M-oster/Advanced-Ultimate-Box-Maker/Examples/Mini-PowerSupply/stls/Adv-Ultimate-Box-PowerSupply-Frontpanel.stl

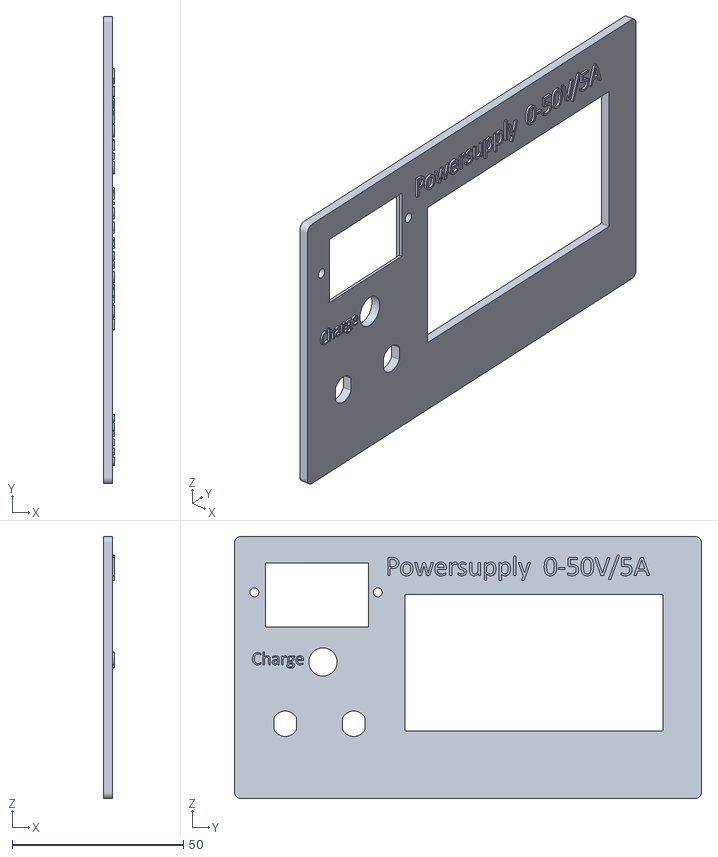
[picture p26: CAD file, 2021-09-02]
Examples/Mini-PowerSupply/stls/Adv-Ultimate-Box-PowerSupply-Frontpanel.stl
3.10 x 136.2 x 76.4
