M-oster/Advanced-Ultimate-Box-Maker/Examples/Mini-PowerSupply/assemblies/dc-dc-5a-cc.FCStd

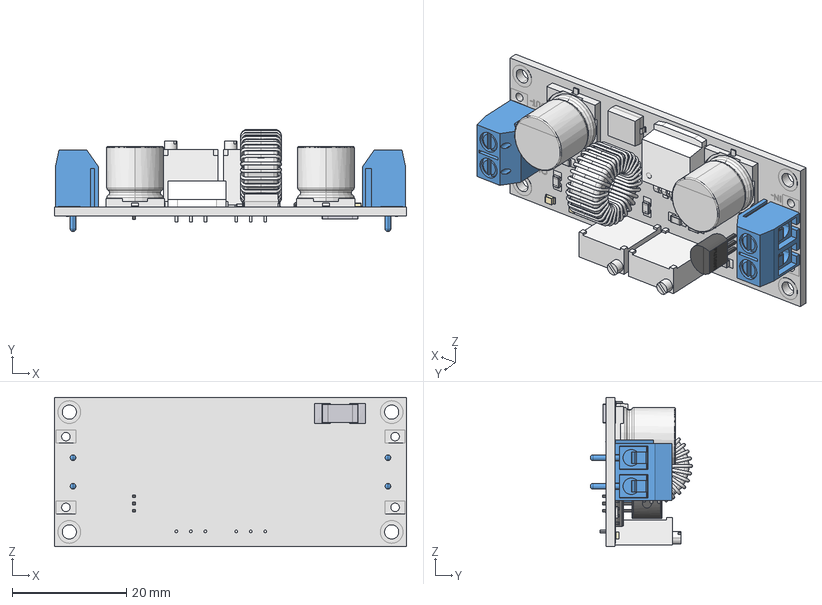
[picture p27: CAD file, 2021-09-02]
Examples/Mini-PowerSupply/assemblies/dc-dc-5a-cc.FCStd
61.7 x 17.9 x 26.2 mm
PCB^dc-dc-5a-cc
DG301-5.0-02
Trimpot 3296W_Valor predeterminado
Trimpot 3296W_Valor predeterminado001
CAPACITOR 10x10 SMD
CAPACITOR 10x10 SMD001
XL4015E1_® 㬮«砭¨뾀
LM317LZ
coil^dc-dc-5a-cc
C
C001
C002
R
R001
R002
R003
R004
LED
LED001
LED002
D
R005
R006
R007
C003
SO-8
Rshunt^dc-dc-5a-cc
DG301-5.0-003
