M-oster/Advanced-Ultimate-Box-Maker/Examples/Mini-PowerSupply/stls/Adv-Ultimate-Box-PowerSupply-Backpanel.stl

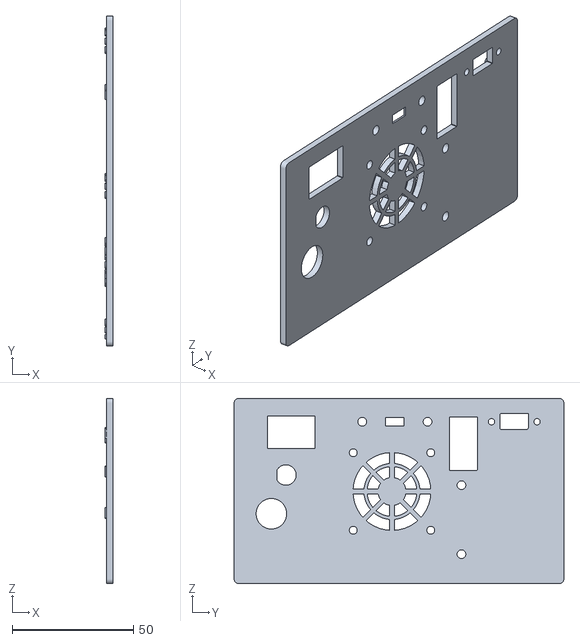
[picture p28: CAD file, 2021-09-02]
Examples/Mini-PowerSupply/stls/Adv-Ultimate-Box-PowerSupply-Backpanel.stl
3.10 x 136.2 x 76.4
