M-oster/Advanced-Ultimate-Box-Maker/Examples/Mini-PowerSupply/assemblies/Relais-Holder.step

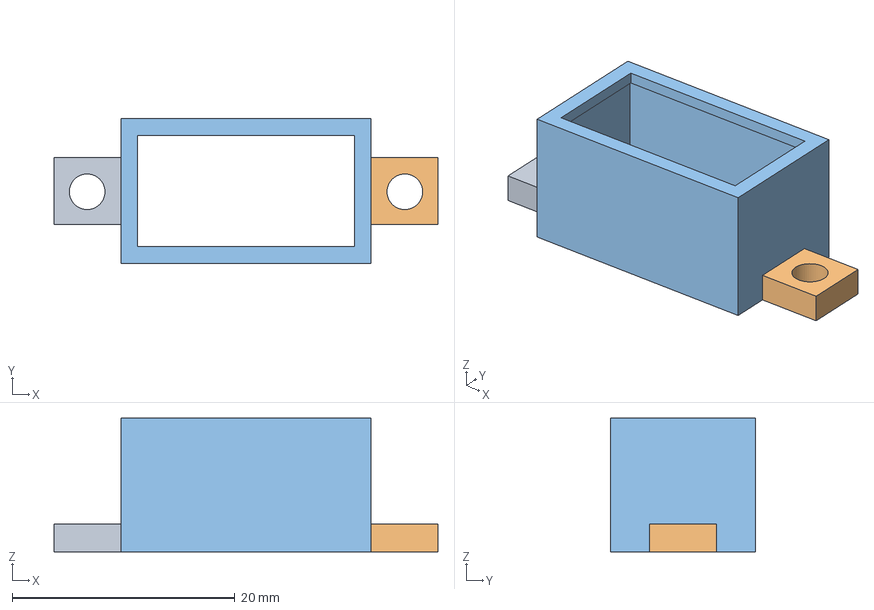
[picture p29: CAD file, 2021-09-02]
Examples/Mini-PowerSupply/assemblies/Relais-Holder.step
34.5 x 13.0 x 12.0 mm
