M-oster/Advanced-Ultimate-Box-Maker/Examples/Mini-PowerSupply/assemblies/LED_5mm+Socket.3mf

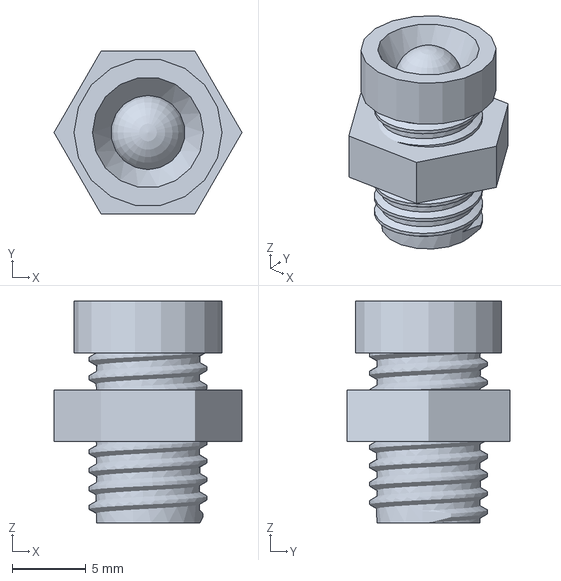
[picture p30: CAD file, 2021-09-02]
Examples/Mini-PowerSupply/assemblies/LED_5mm+Socket.3mf
12.7 x 11.0 x 15.0 mm
