M-oster/Advanced-Ultimate-Box-Maker/Examples/Mini-PowerSupply/assemblies/BT-Modul_BK3231.step

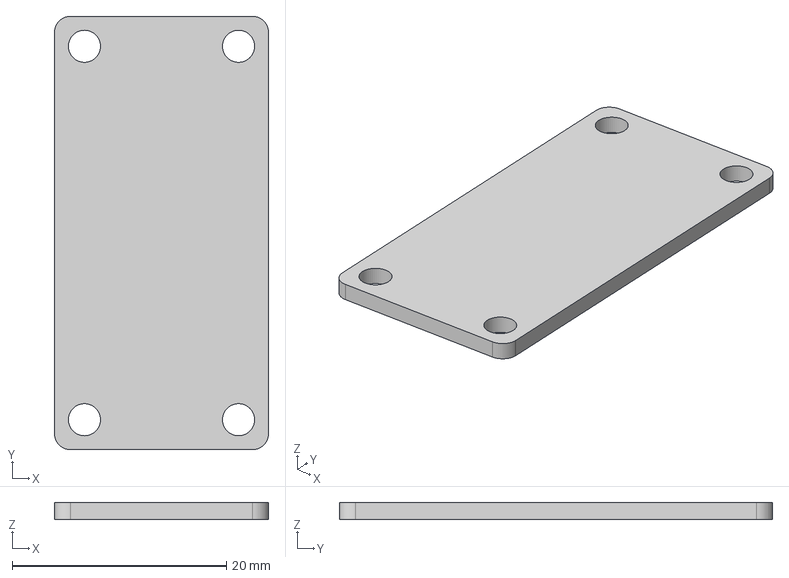
[picture p31: CAD file, 2021-09-02]
Examples/Mini-PowerSupply/assemblies/BT-Modul_BK3231.step
20.0 x 40.5 x 1.60 mm
