M-oster/Advanced-Ultimate-Box-Maker/Examples/Mini-PowerSupply/assemblies/PowerJackNut.step

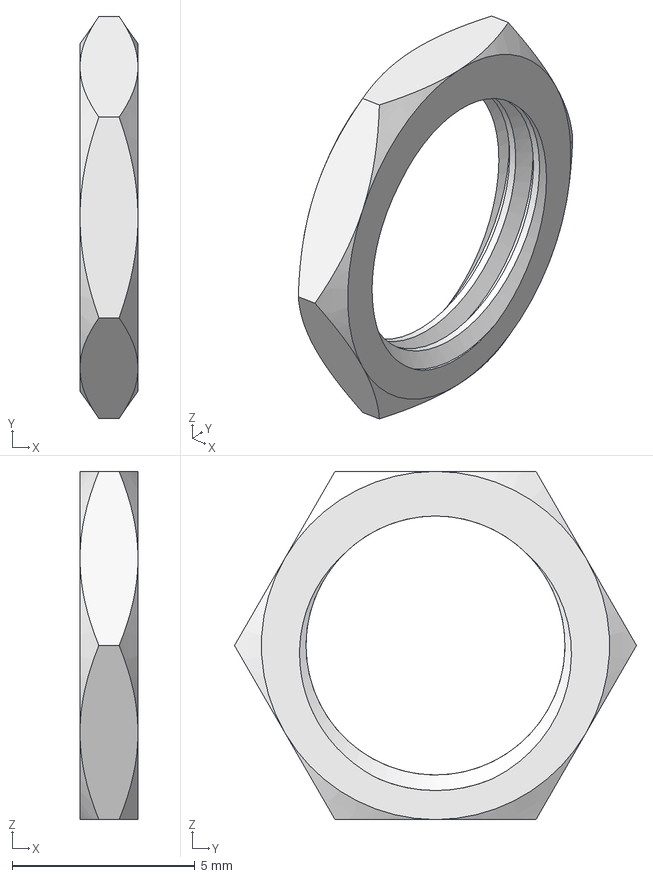
[picture p32: CAD file, 2021-09-02]
Examples/Mini-PowerSupply/assemblies/PowerJackNut.step
1.59 x 11.0 x 9.52 mm
