M-oster/Advanced-Ultimate-Box-Maker/Examples/Mini-PowerSupply/assemblies/AutomFuseholder.step

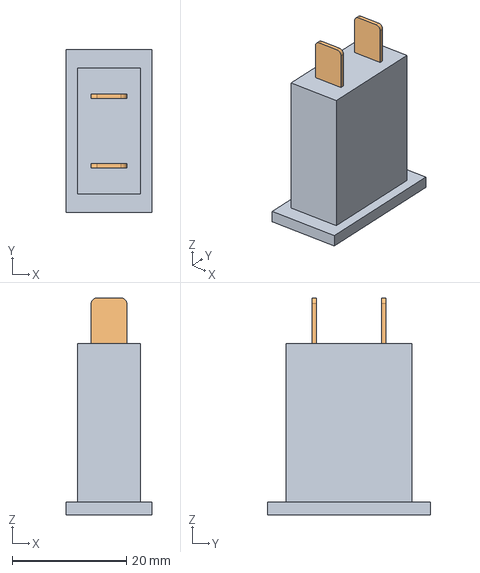
[picture p33: CAD file, 2021-09-02]
Examples/Mini-PowerSupply/assemblies/AutomFuseholder.step
15.1 x 28.5 x 38.0 mm
