M-oster/Advanced-Ultimate-Box-Maker/Examples/Mini-PowerSupply/assemblies/BATTERY-HOLDER_18650.stl

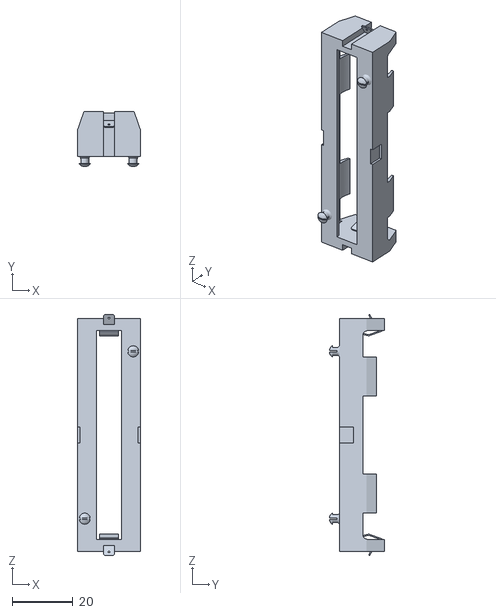
[picture p34: CAD file, 2021-09-02]
Examples/Mini-PowerSupply/assemblies/BATTERY-HOLDER_18650.stl
20.7 x 18.3 x 79.5
