M-oster/Advanced-Ultimate-Box-Maker/Examples/Mini-PowerSupply/assemblies/USB-Module_CH340G.step

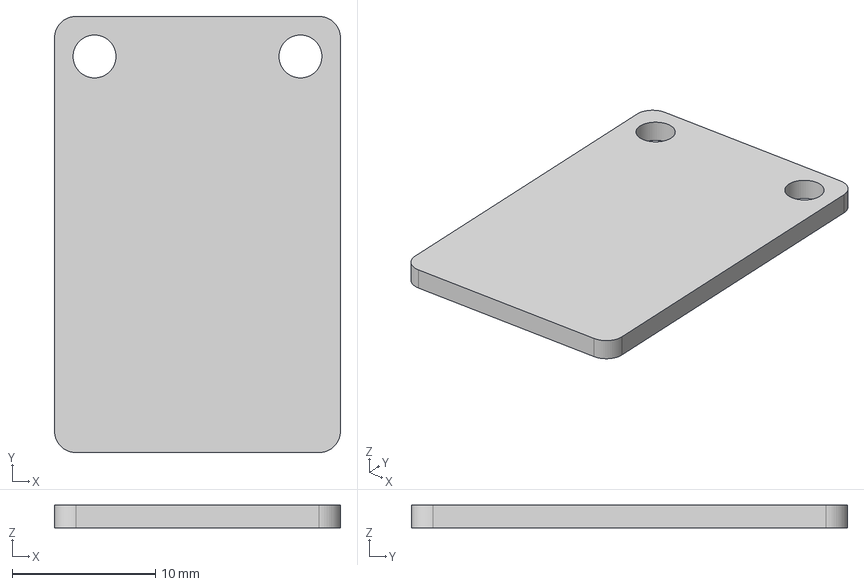
[picture p35: CAD file, 2021-09-02]
Examples/Mini-PowerSupply/assemblies/USB-Module_CH340G.step
20.0 x 30.5 x 1.60 mm
